bkw777/TANDY_600_RAM/PCB/out/TANDY_600_RAM_DUAL.jpg

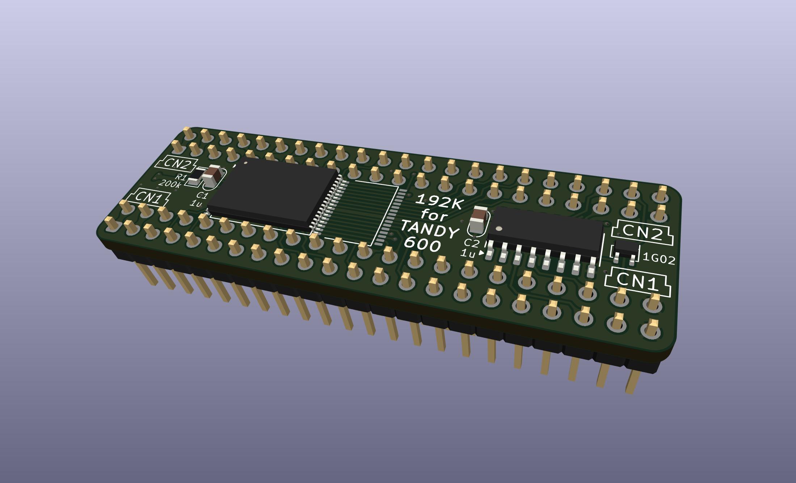
PCB/out/TANDY_600_RAM_DUAL.jpg
